m-a-r-k-d/slit_grating_spectrometer/ray_trace/beamfour_files/Curvatures_SF2.png

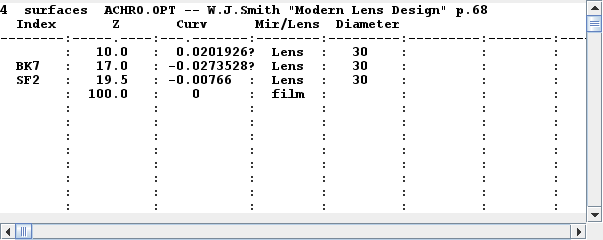
ray_trace/beamfour_files/Curvatures_SF2.png
